BoujeeEnjinia1701/canalrung/cad/drawings/CNR-DWG-001.png

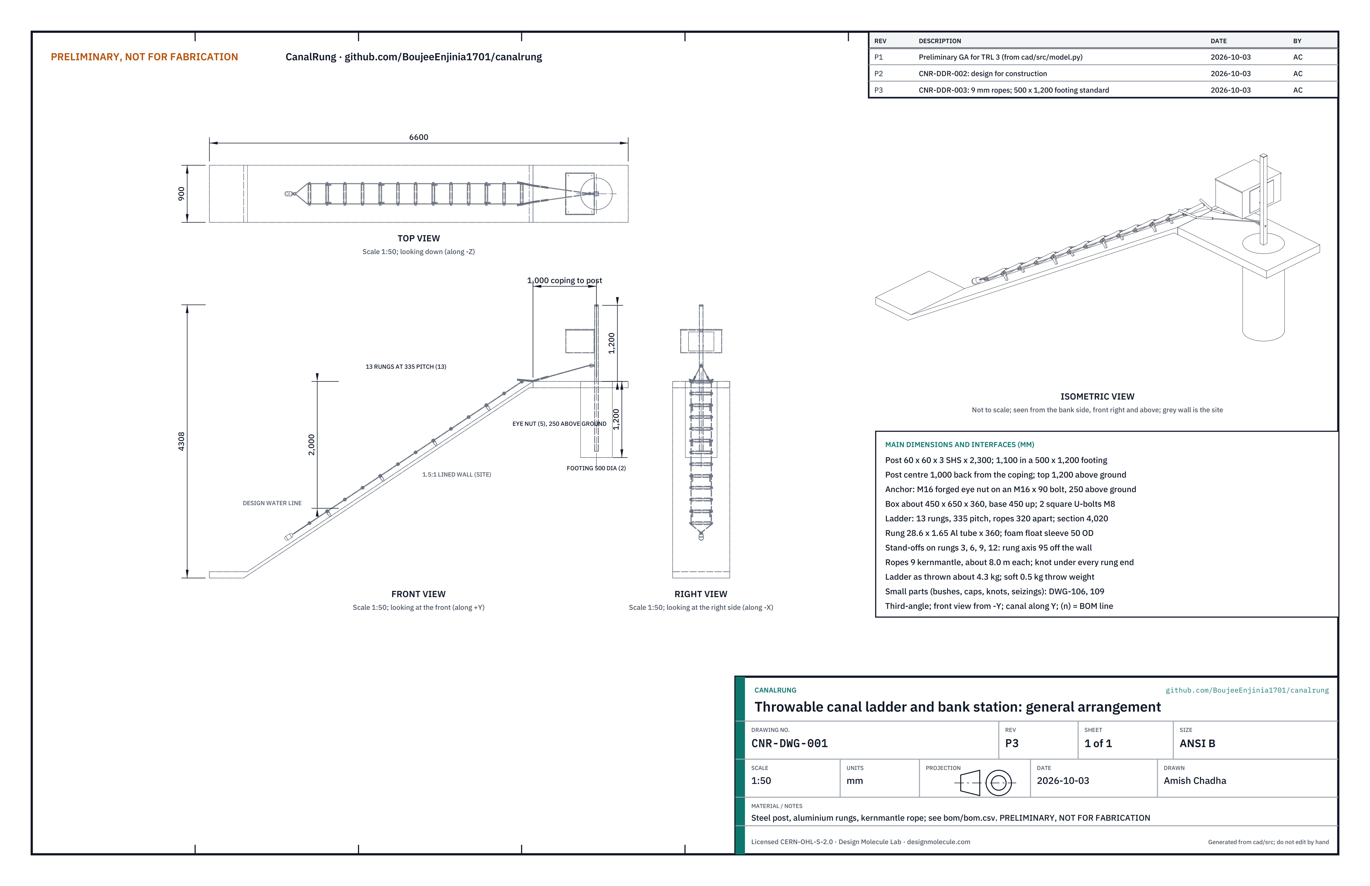
cad/drawings/CNR-DWG-001.png
