BoujeeEnjinia1701/canalrung/media/card.png

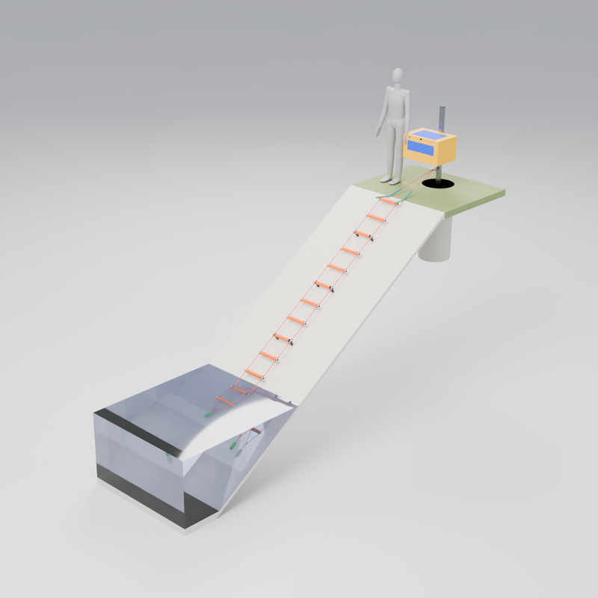
media/card.png
