BoujeeEnjinia1701/canalrung/media/render-detail.png

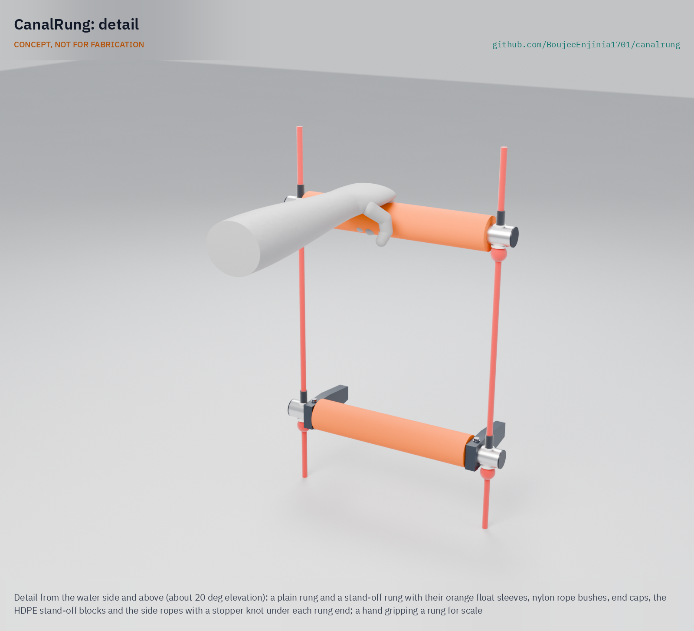
media/render-detail.png
