BoujeeEnjinia1701/canalrung/media/render-exploded.png

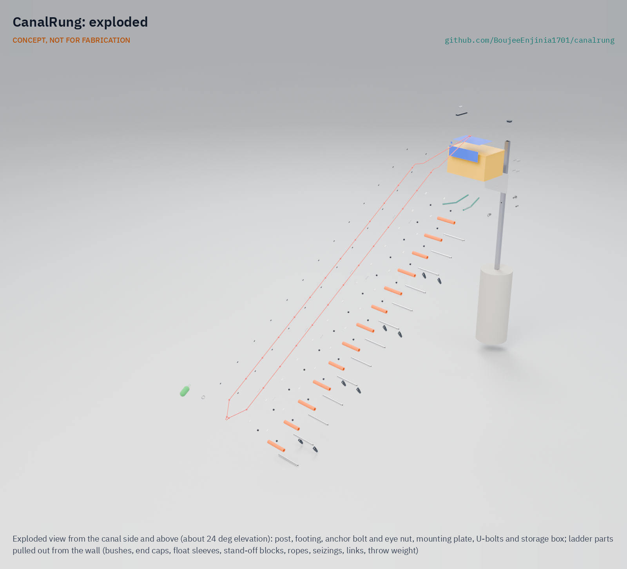
media/render-exploded.png
