BoujeeEnjinia1701/canalrung/media/social-preview.png

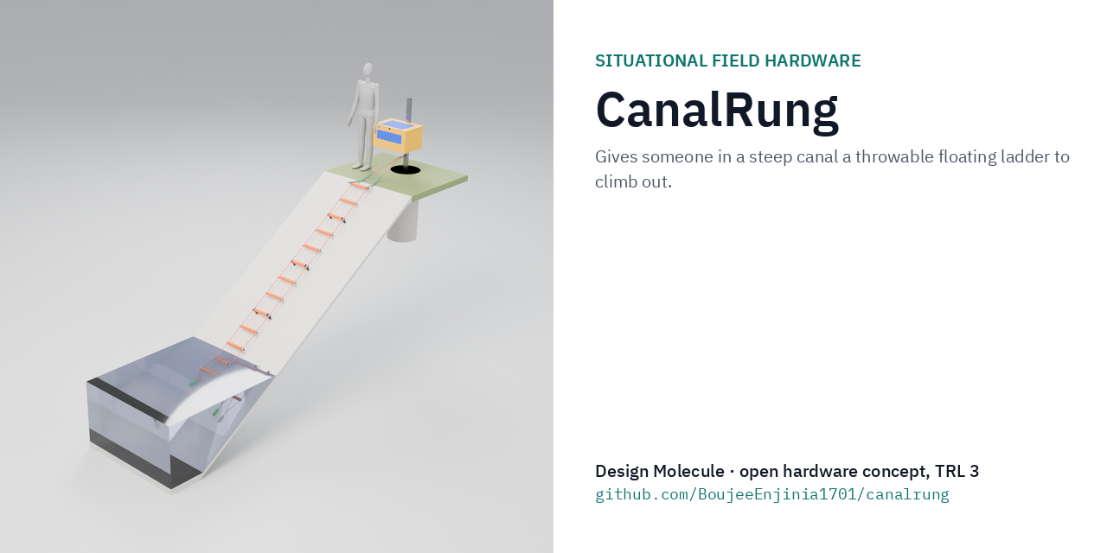
media/social-preview.png
